hspsh/ErgoCogs/GearBoxes/ErgoDOX Acrylic Case - Designed by Litster/Standard/Right/ErgoDOX Case Layer 4 Spacer - Right.dxf

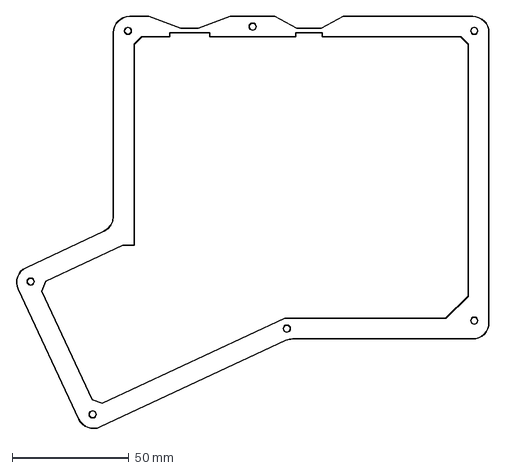
[picture p19: CAD file, 2021-06-02]
GearBoxes/ErgoDOX Acrylic Case - Designed by Litster/Standard/Right/ErgoDOX Case Layer 4 Spacer - Right.dxf
202.8 x 177.8 mm
