hspsh/ErgoCogs/GearBoxes/ErgoDOX Acrylic Case - Designed by Litster/with Wrist Rest/Left/ErgoDOX Case Layer 4 Spacer - Left.dxf

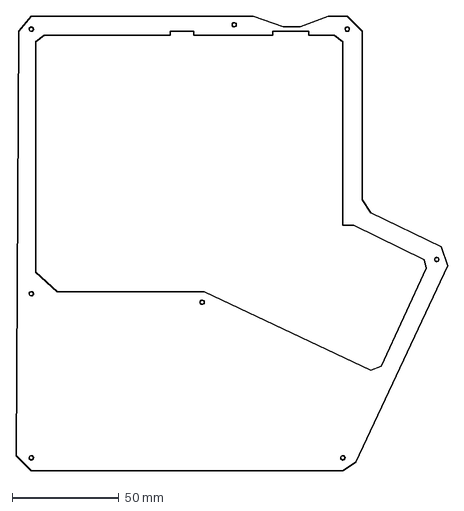
[picture p20: CAD file, 2021-06-02]
GearBoxes/ErgoDOX Acrylic Case - Designed by Litster/with Wrist Rest/Left/ErgoDOX Case Layer 4 Spacer - Left.dxf
202.0 x 213.0 mm
