hspsh/ErgoCogs/GearBoxes/ErgoDOX Acrylic Case - Designed by Litster/with Wrist Rest/Right/ErgoDOX Wrist Rest Case Layer 2 Spacer - Right.dxf

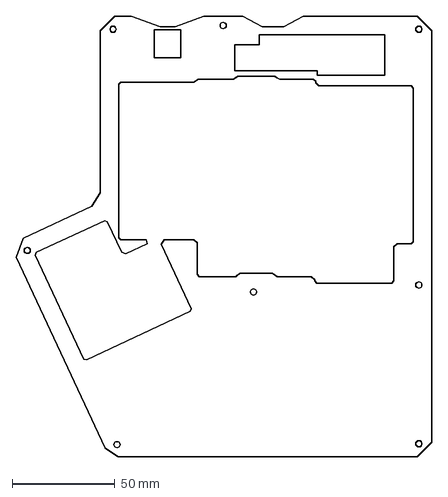
[picture p21: CAD file, 2021-06-02]
GearBoxes/ErgoDOX Acrylic Case - Designed by Litster/with Wrist Rest/Right/ErgoDOX Wrist Rest Case Layer 2 Spacer - Right.dxf
202.0 x 214.1 mm
