hspsh/ErgoCogs/GearBoxes/ErgoCogs_integrated/plate.stl

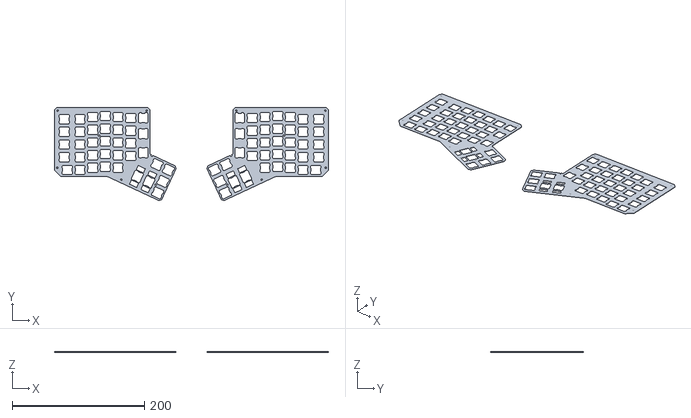
[picture p22: CAD file, 2021-06-14]
GearBoxes/ErgoCogs_integrated/plate.stl
414.9 x 141.1 x 1.56
