hspsh/ErgoCogs/GearBoxes/ErgoDOX Acrylic Case - Designed by Litster/Standard/Left/ErgoDOX Case Layer 4 Spacer - Left.dxf

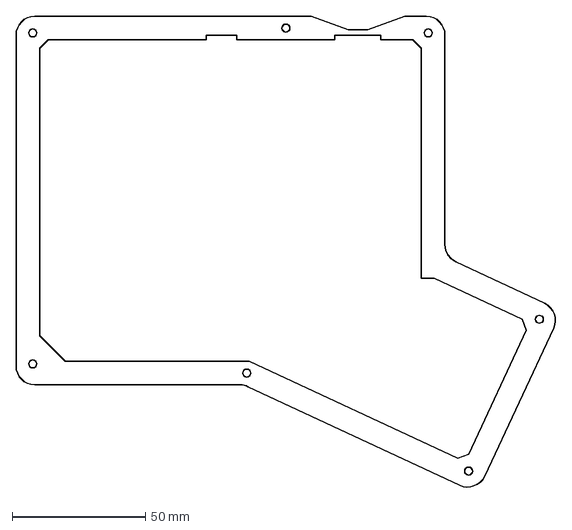
[picture p23: CAD file, 2021-06-02]
GearBoxes/ErgoDOX Acrylic Case - Designed by Litster/Standard/Left/ErgoDOX Case Layer 4 Spacer - Left.dxf
202.8 x 177.8 mm
