hspsh/ErgoCogs/GearBoxes/ErgoDOX Acrylic Case - Designed by Litster/Standard/Right/ErgoDOX Case Layer 1 Top - Right.dxf

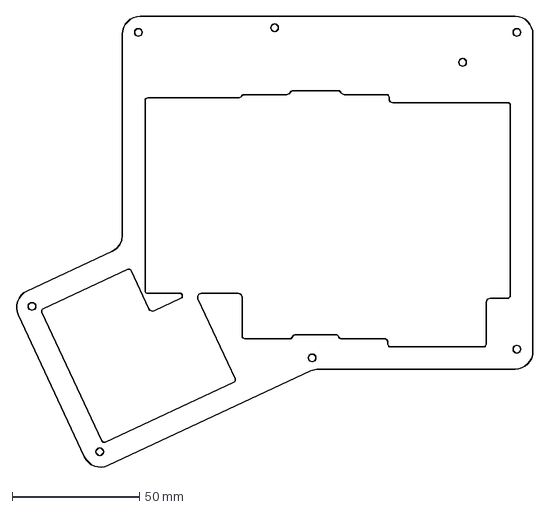
[picture p24: CAD file, 2021-06-02]
GearBoxes/ErgoDOX Acrylic Case - Designed by Litster/Standard/Right/ErgoDOX Case Layer 1 Top - Right.dxf
202.8 x 177.8 mm
