hspsh/ErgoCogs/GearBoxes/ErgoDOX Acrylic Case - Designed by Litster/with Wrist Rest/Left/ErgoDOX Case Layer 3 Plate - Left.dxf

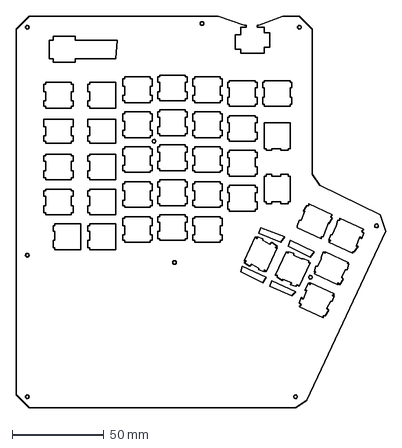
[picture p25: CAD file, 2021-06-02]
GearBoxes/ErgoDOX Acrylic Case - Designed by Litster/with Wrist Rest/Left/ErgoDOX Case Layer 3 Plate - Left.dxf
201.0 x 213.0 mm
