hspsh/ErgoCogs/GearBoxes/ErgoCogs_integrated/plate_sample.stl

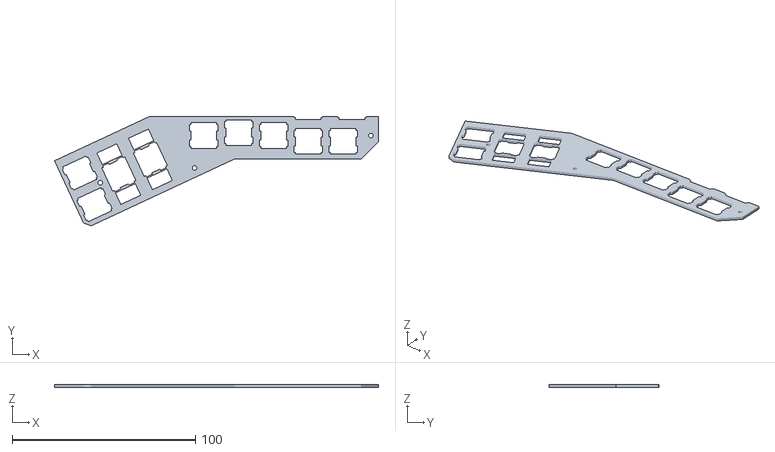
[picture p27: CAD file, 2021-06-14]
GearBoxes/ErgoCogs_integrated/plate_sample.stl
177.0 x 59.9 x 1.55
