hspsh/ErgoCogs/GearBoxes/ErgoDOX Acrylic Case - Designed by Litster/with Wrist Rest/Left/ErgoDOX Case Layer 2 Spacer - Left.dxf

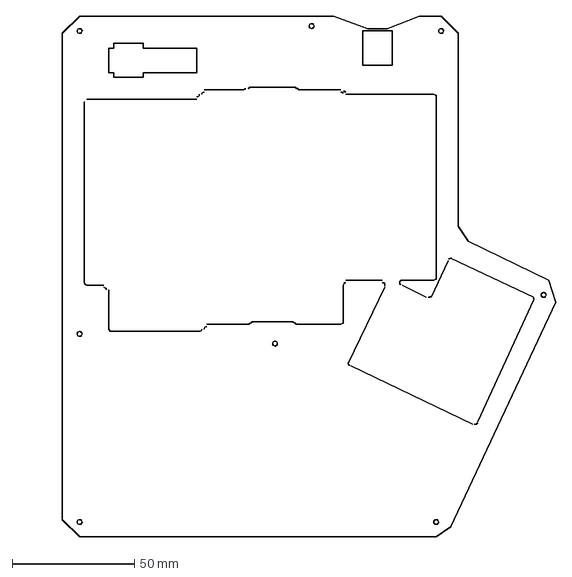
[picture p30: CAD file, 2021-06-02]
GearBoxes/ErgoDOX Acrylic Case - Designed by Litster/with Wrist Rest/Left/ErgoDOX Case Layer 2 Spacer - Left.dxf
221.0 x 213.0 mm
