hspsh/ErgoCogs/GearBoxes/ErgoCogs_integrated/brain_bigger_outline.dxf

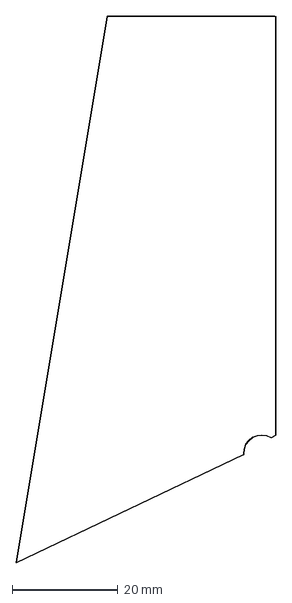
[picture p32: CAD file, 2021-06-14]
GearBoxes/ErgoCogs_integrated/brain_bigger_outline.dxf
49.1 x 103.2 mm
