hspsh/ErgoCogs/GearBoxes/ErgoCogs_integrated/mount_holes.dxf

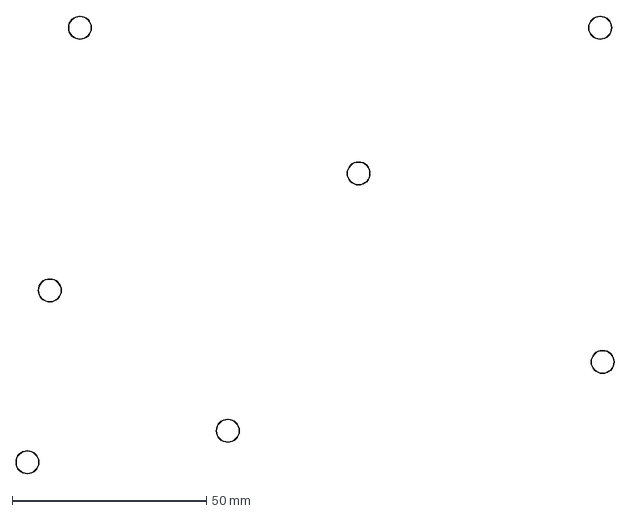
[picture p34: CAD file, 2021-06-14]
GearBoxes/ErgoCogs_integrated/mount_holes.dxf
153.7 x 117.6 mm
