hspsh/ErgoCogs/GearBoxes/ErgoCogs_integrated/plate_outline.dxf

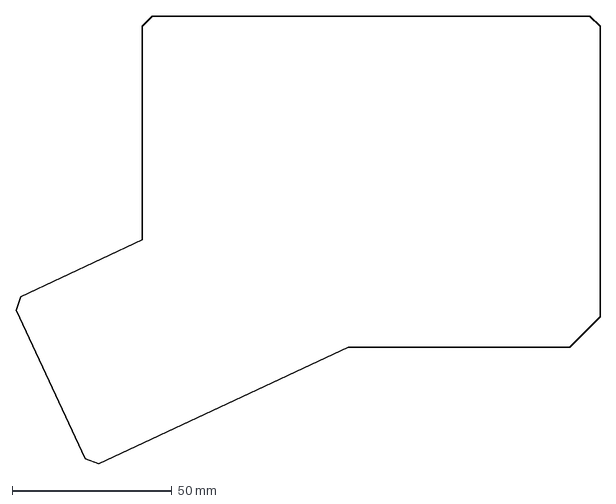
[picture p35: CAD file, 2021-06-14]
GearBoxes/ErgoCogs_integrated/plate_outline.dxf
182.8 x 140.1 mm
