hspsh/ErgoCogs/GearBoxes/ErgoCogs_integrated/all.stl

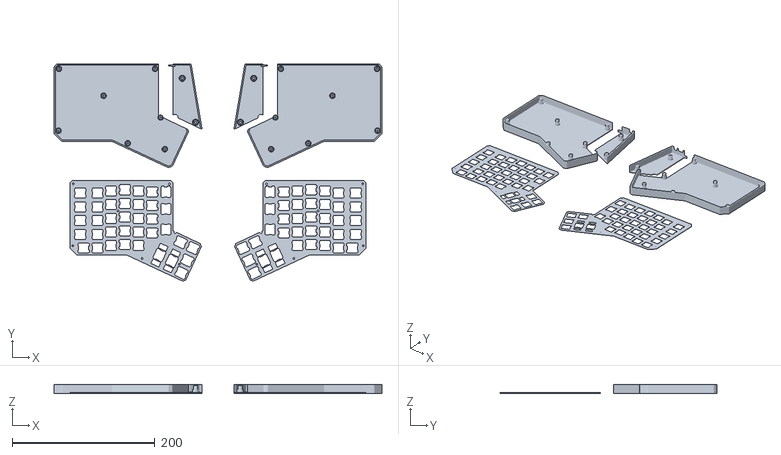
[picture p36: CAD file, 2021-06-14]
GearBoxes/ErgoCogs_integrated/all.stl
459.4 x 304.4 x 12.7
