hspsh/ErgoCogs/GearBoxes/ErgoCogs_integrated/brain_outline.dxf

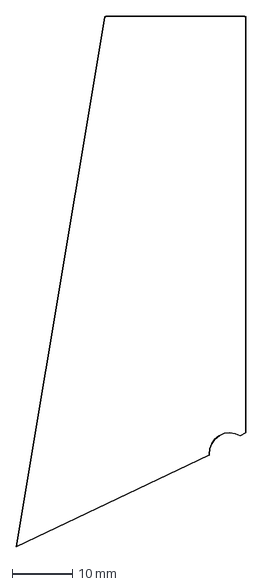
[picture p37: CAD file, 2021-06-14]
GearBoxes/ErgoCogs_integrated/brain_outline.dxf
38.1 x 88.0 mm
