hspsh/ErgoCogs/GearBoxes/ErgoCogs_integrated/brain_holes.dxf

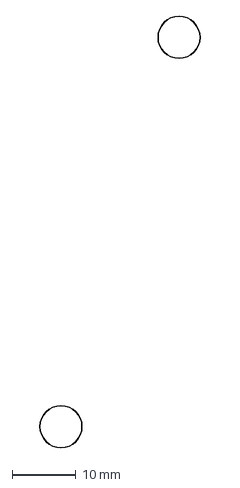
[picture p38: CAD file, 2021-06-14]
GearBoxes/ErgoCogs_integrated/brain_holes.dxf
25.1 x 67.6 mm
