hspsh/ErgoCogs/GearBoxes/ErgoCogs_integrated/bottom.stl

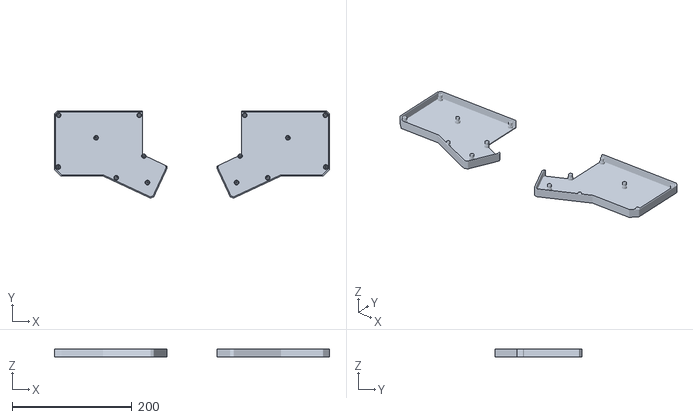
[picture p39: CAD file, 2021-06-14]
GearBoxes/ErgoCogs_integrated/bottom.stl
459.4 x 145.3 x 12.7
