hspsh/ErgoCogs/GearBoxes/ErgoCogs_integrated/outer_outline.dxf

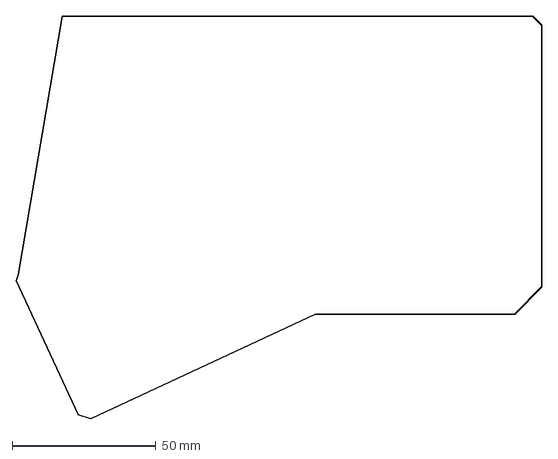
[picture p40: CAD file, 2021-06-14]
GearBoxes/ErgoCogs_integrated/outer_outline.dxf
182.8 x 140.1 mm
