hspsh/ErgoCogs/GearBoxes/ErgoCogs_integrated/plate_cutouts.dxf

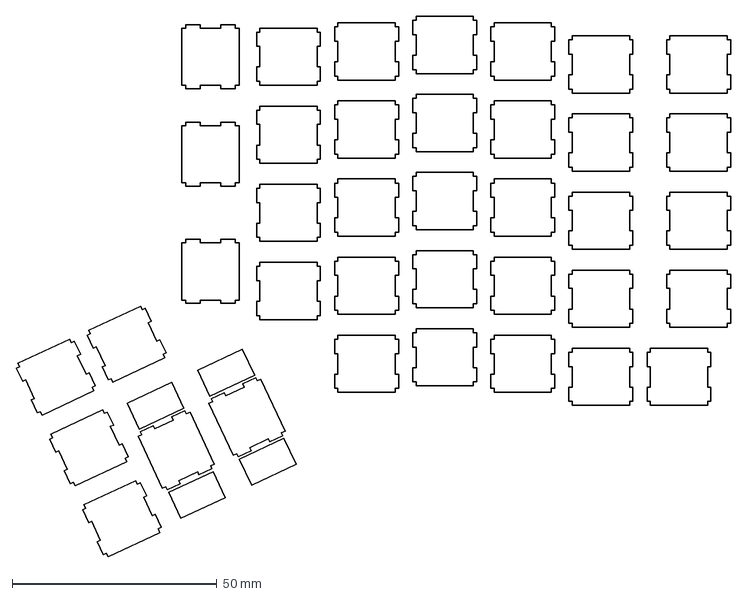
[picture p41: CAD file, 2021-06-14]
GearBoxes/ErgoCogs_integrated/plate_cutouts.dxf
174.2 x 131.8 mm
