hspsh/ErgoCogs/GearBoxes/ErgoCogs_integrated/brain_bottom.stl

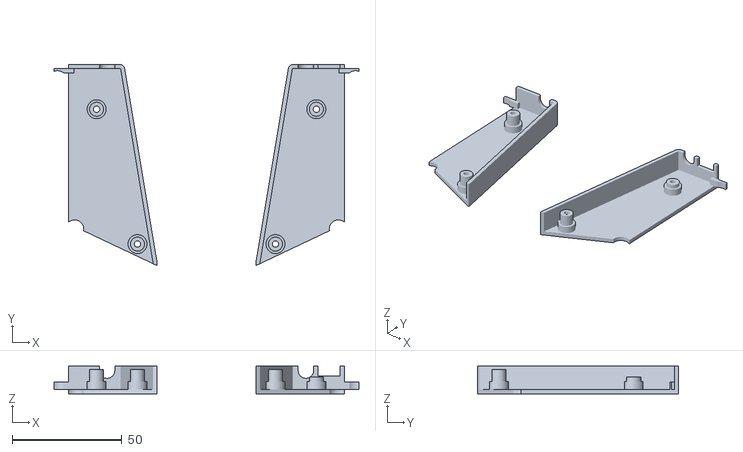
[picture p42: CAD file, 2021-06-14]
GearBoxes/ErgoCogs_integrated/brain_bottom.stl
139.0 x 91.6 x 12.7
